HyacinthSat/High-Altitude-Balloons/2025.07.06/2025-07-06_19-34-27.jpg

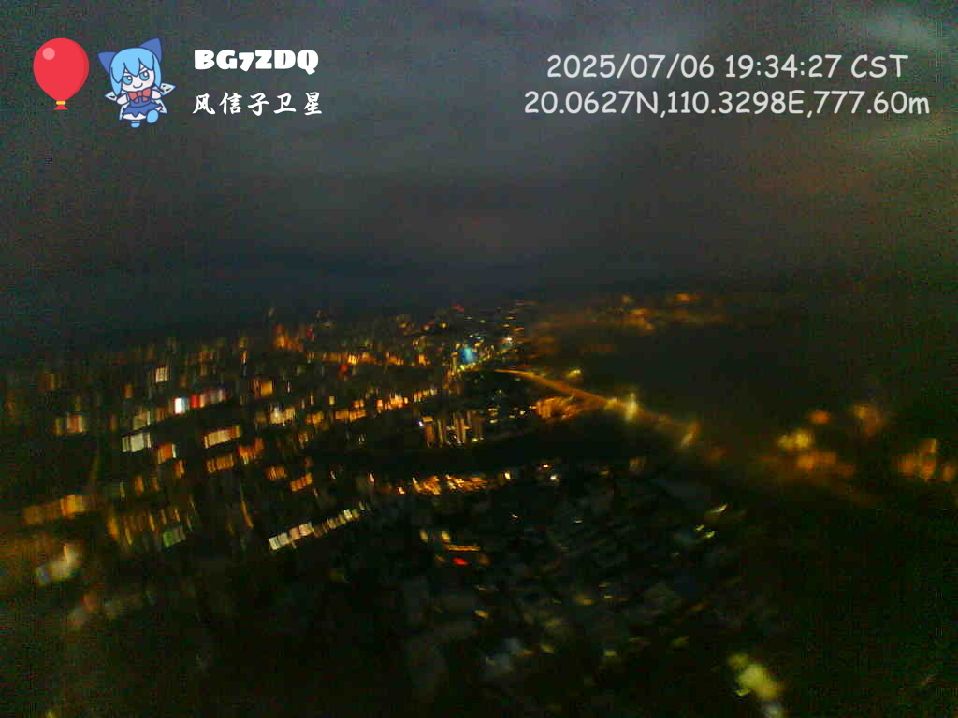
2025.07.06/2025-07-06_19-34-27.jpg
