HyacinthSat/High-Altitude-Balloons/2025.07.06/2025-07-06_19-37-55.jpg

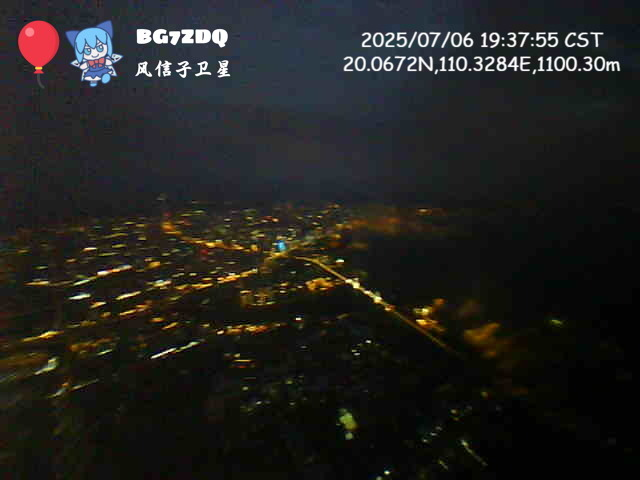
2025.07.06/2025-07-06_19-37-55.jpg
