HyacinthSat/High-Altitude-Balloons/2025.07.06/2025-07-06_19-39-45.jpg

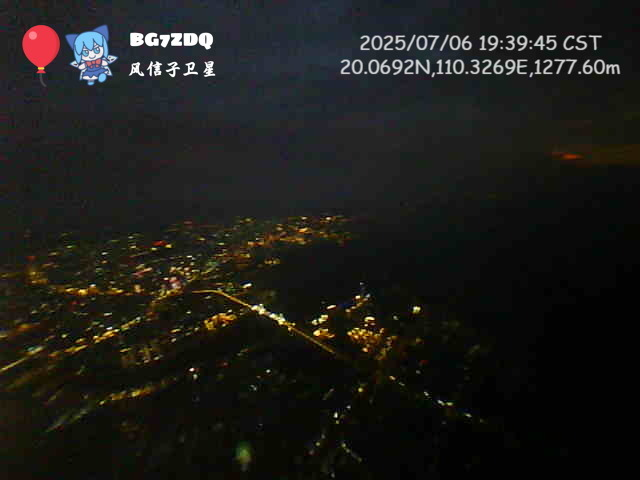
2025.07.06/2025-07-06_19-39-45.jpg
