HyacinthSat/High-Altitude-Balloons/2025.07.06/2025-07-06_19-40-09.jpg

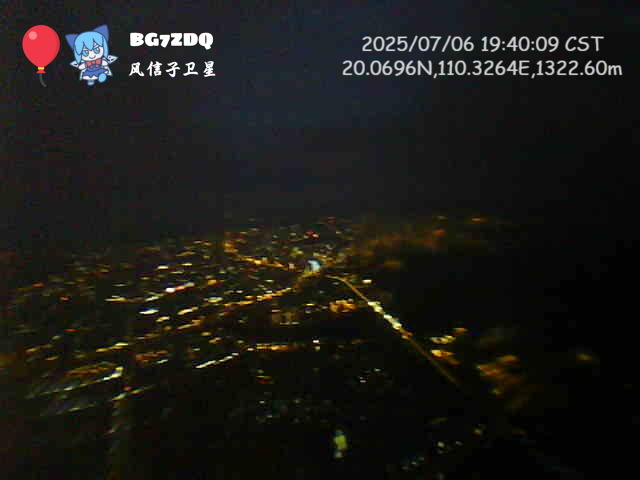
2025.07.06/2025-07-06_19-40-09.jpg
