HyacinthSat/High-Altitude-Balloons/2025.07.06/2025-07-06_21-10-39.jpg

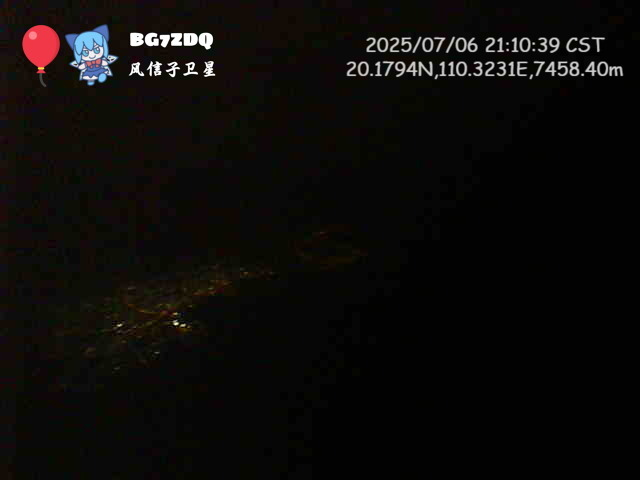
2025.07.06/2025-07-06_21-10-39.jpg
