HyacinthSat/High-Altitude-Balloons/2025.07.06/original_image/2025-07-06_19-27-22.jpg

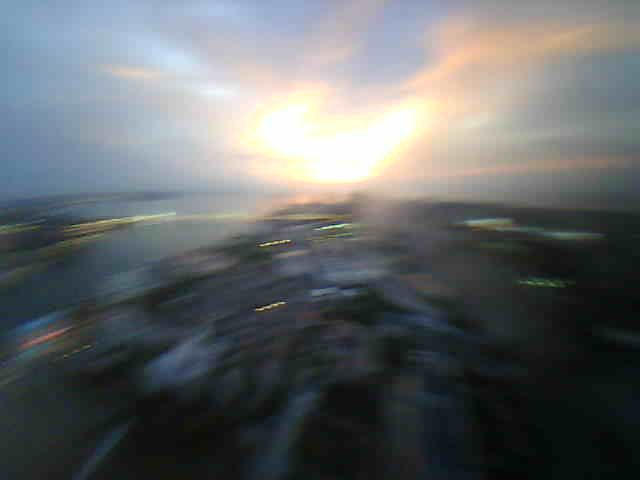
2025.07.06/original_image/2025-07-06_19-27-22.jpg
