HyacinthSat/High-Altitude-Balloons/2025.07.06/original_image/2025-07-06_22-11-47.jpg

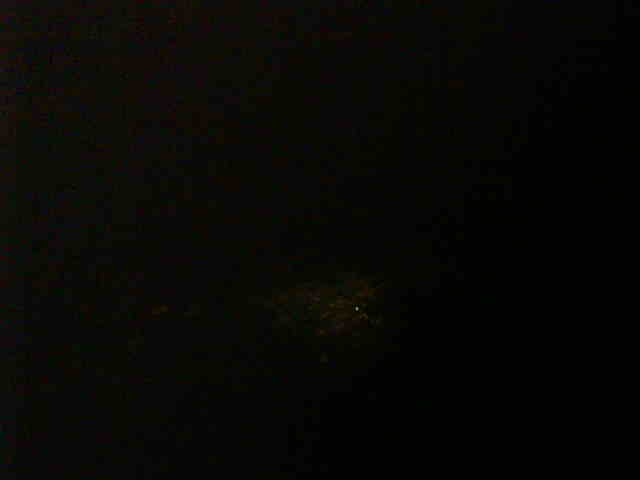
2025.07.06/original_image/2025-07-06_22-11-47.jpg
