HyacinthSat/High-Altitude-Balloons/2025.07.06/original_image/d2025-07-06_20-15-10.jpg

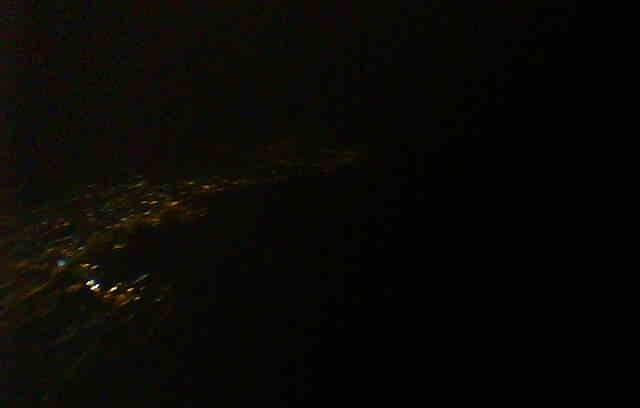
2025.07.06/original_image/d2025-07-06_20-15-10.jpg
