HyacinthSat/High-Altitude-Balloons/2025.07.06/信噪比测量 2025-07-06 215317.png

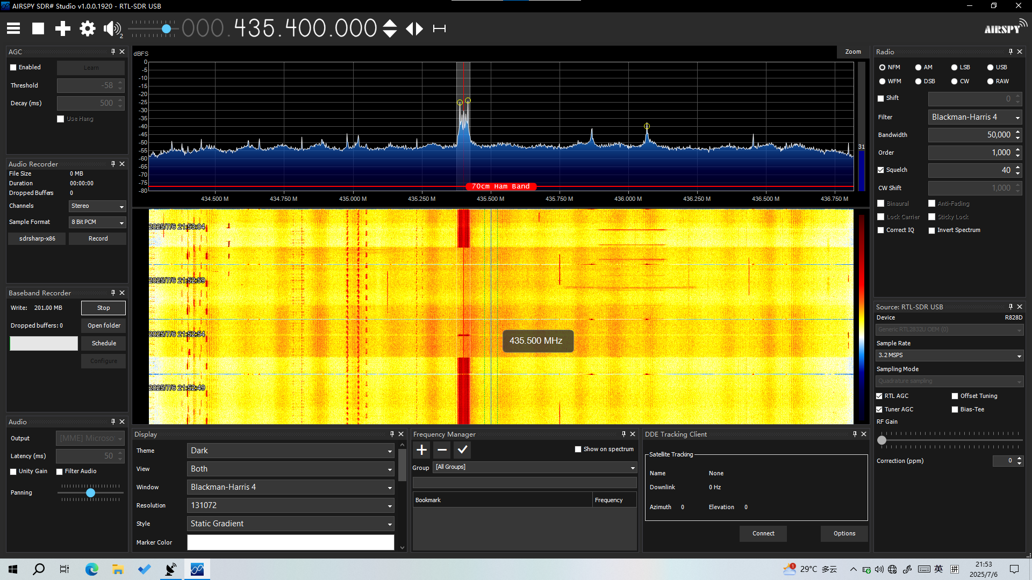
2025.07.06/信噪比测量 2025-07-06 215317.png
