HyacinthSat/High-Altitude-Balloons/Balloon/data/preset_1.jpg

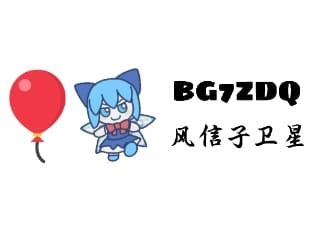
Balloon/data/preset_1.jpg
