HyacinthSat/High-Altitude-Balloons/Balloon/data/preset_2.jpg

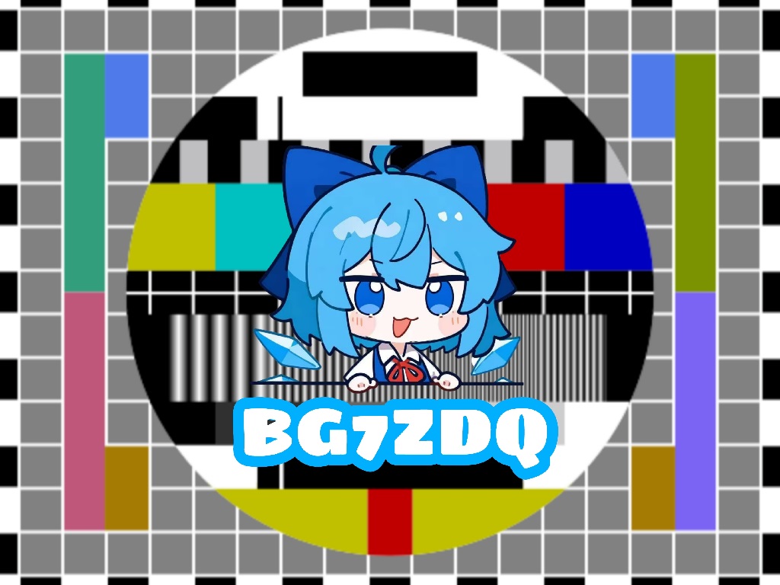
Balloon/data/preset_2.jpg
