HyacinthSat/High-Altitude-Balloons/Balloon/data/preset_3.jpg

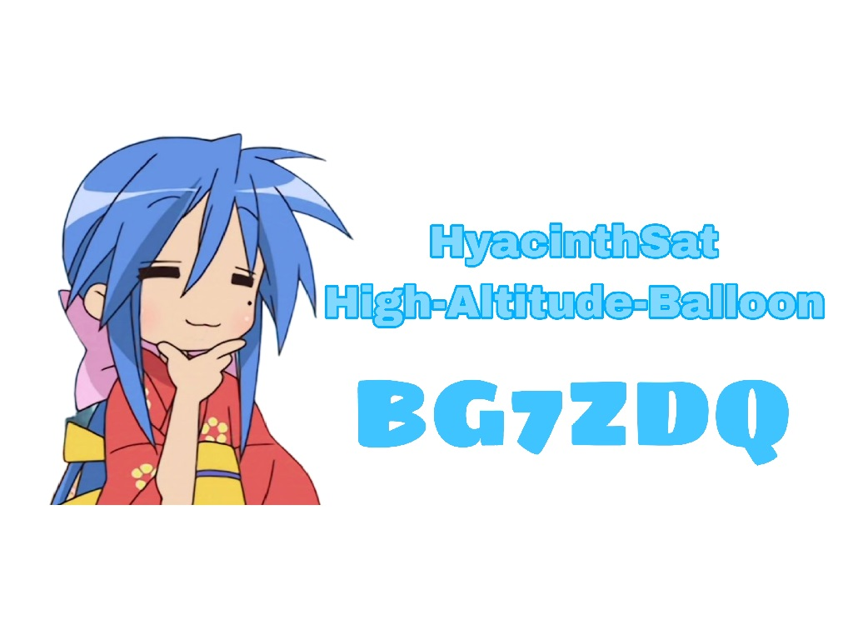
Balloon/data/preset_3.jpg
